caedm/wall-ink/stream_screen/debug_mode.h

#include <pgmspace.h>

const unsigned char debug_image[] PROGMEM = {
0xff,0xff,0xff,0xff,0xff,0xff,0xff,0xff,0xff,0xff,0xff,0xff,0xff,0xff,0xff,0xff,
0xff,0xff,0xff,0xff,0xff,0xff,0xff,0xff,0xff,0xff,0xff,0xff,0xff,0xff,0xff,0xff,
0xff,0xff,0xff,0xff,0xff,0xff,0xff,0xff,0xff,0xff,0xff,0xff,0xff,0xff,0xff,0xff,
0xff,0xff,0xff,0xff,0xff,0xff,0xff,0xff,0xff,0xff,0xff,0xff,0xff,0xff,0xff,0xff,
0xff,0xff,0xff,0xff,0xff,0xff,0xff,0xff,0xff,0xff,0xff,0xff,0xff,0xff,0xff,0xff,
0xff,0xff,0xff,0xff,0xff,0xff,0xff,0xff,0xff,0xff,0xff,0xff,0xff,0xff,0xff,0xff,
0xff,0xff,0xff,0xff,0xff,0xff,0xff,0xff,0xff,0xff,0xff,0xff,0xff,0xff,0xff,0xff,
0xff,0xff,0xff,0xff,0xff,0xff,0xff,0xff,0xff,0xff,0xff,0xff,0xff,0xff,0xff,0xff,
0xff,0xff,0xff,0xff,0xff,0xff,0xff,0xf8,0xff,0xff,0xff,0xff,0xff,0xff,0xff,0xff,
0xff,0xff,0xff,0xff,0xff,0xff,0xff,0xff,0xff,0xff,0xff,0xff,0xff,0xff,0xff,0xff,
0xff,0xff,0xff,0xff,0xff,0xff,0xff,0xff,0xff,0xff,0xff,0xff,0xff,0xff,0xff,0xff,
0xff,0xff,0xff,0xff,0xff,0xff,0xff,0xff,0xff,0xff,0xff,0xff,0xff,0xff,0xff,0xff,
0xff,0xff,0xff,0xff,0xff,0xff,0xff,0xff,0xff,0xff,0xff,0xff,0xff,0xff,0xbf,0xff,
0xff,0xff,0xff,0xff,0xff,0xff,0xff,0xf7,0xff,0xff,0xff,0xff,0xff,0xff,0xff,0xff,
0xff,0xff,0xff,0xff,0xff,0xff,0xff,0xff,0xff,0xff,0xff,0xff,0xff,0xff,0xff,0xff,
0xff,0xff,0xff,0xff,0xff,0xff,0xff,0xff,0xff,0xff,0xff,0xff,0xff,0xff,0xff,0xff,
0xff,0xff,0xff,0xff,0xff,0x0c,0x30,0xe1,0xfe,0x38,0xc1,0x8e,0x38,0xff,0x3c,0x3f,
0xe3,0x0e,0x3f,0x43,0x87,0xf8,0xcf,0xfc,0xf8,0xc3,0x75,0xd8,0xe3,0xff,0x70,0xf7,
0x8c,0xf8,0xc3,0xfc,0x30,0xe3,0x57,0xf0,0xc3,0x84,0x3c,0x7f,0xff,0xff,0xff,0xff,
0xff,0xff,0xff,0xff,0xff,0xff,0xff,0xff,0xff,0xff,0xff,0xff,0xff,0xff,0xff,0xff,
0xff,0xff,0xff,0xff,0xff,0xff,0xff,0xff,0xff,0xff,0xff,0xff,0xff,0xff,0xff,0xff,
0xff,0xff,0xff,0xff,0xff,0x75,0xd7,0x5d,0xfd,0xd7,0x7b,0x77,0x7d,0xff,0xdd,0xdf,
0xf7,0x77,0x7f,0x7d,0x7f,0xf7,0x77,0xff,0x77,0x7d,0x75,0xd7,0x5d,0xff,0x7f,0x77,
0xdf,0x77,0x5d,0xff,0xd7,0x5d,0x57,0xf7,0x5d,0x77,0xdb,0x7f,0xff,0xff,0xff,0xff,
0xff,0xff,0xff,0xff,0xff,0xff,0xff,0xff,0xff,0xff,0xff,0xff,0xff,0xff,0xff,0xff,
0xff,0xff,0xff,0xff,0xff,0xff,0xff,0xff,0xff,0xff,0xff,0xff,0xff,0xff,0xff,0xff,
0xff,0xff,0xff,0xff,0xff,0x75,0xd7,0x5d,0xfd,0xd7,0x77,0x7f,0x7d,0xff,0xdd,0xdf,
0xf7,0x77,0x7f,0x7d,0x7f,0xf7,0x77,0xff,0x7f,0x7d,0x75,0xd7,0x7d,0xff,0xff,0x6b,
0xdf,0x7f,0x5d,0xff,0xd7,0x5d,0x57,0xf7,0x5d,0x77,0xd7,0x7f,0xff,0xff,0xff,0xff,
0xff,0xff,0xff,0xff,0xff,0xff,0xff,0xff,0xff,0xff,0xff,0xff,0xff,0xff,0xff,0xff,
0xff,0xff,0xff,0xff,0xff,0xff,0xff,0xff,0xff,0xff,0xff,0xff,0xff,0xff,0xff,0xff,
0xff,0xff,0xff,0xff,0xff,0x75,0xd0,0xdd,0xfd,0x96,0x6f,0x7f,0x7d,0xff,0xdc,0x3f,
0xf7,0x0f,0x7f,0x41,0x8f,0xf7,0x77,0xff,0x7f,0x41,0x75,0xd7,0x7d,0xff,0xf0,0x6b,
0xdf,0x7f,0x43,0xfc,0x17,0x5d,0x57,0xf7,0x5d,0x74,0x17,0x7f,0xff,0xff,0xff,0xff,
0xff,0xff,0xff,0xff,0xff,0xff,0xff,0xff,0xff,0xff,0xff,0xff,0xff,0xff,0xff,0xff,
0xff,0xff,0xff,0xff,0xff,0xff,0xff,0xff,0xff,0xff,0xff,0xff,0xff,0xff,0xff,0xff,
0xff,0xff,0xff,0xff,0xff,0x75,0xd7,0xdd,0xfd,0x55,0x5f,0x87,0x7d,0xff,0xdd,0xff,
0xf7,0x7f,0x7e,0x5d,0xf7,0xf7,0x77,0xff,0x77,0x5d,0x75,0xd7,0x5d,0xff,0x77,0x5d,
0xdf,0x77,0x5f,0xfd,0xd7,0x5d,0x57,0xf7,0x5d,0x75,0xd7,0x7f,0xff,0xff,0xff,0xff,
0xff,0xff,0xff,0xff,0xff,0xff,0xff,0xff,0xff,0xff,0xff,0xff,0xff,0xff,0xff,0xff,
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
